SkyePooley/ENEL599-Final-Project/Images/20231011_123835.jpg

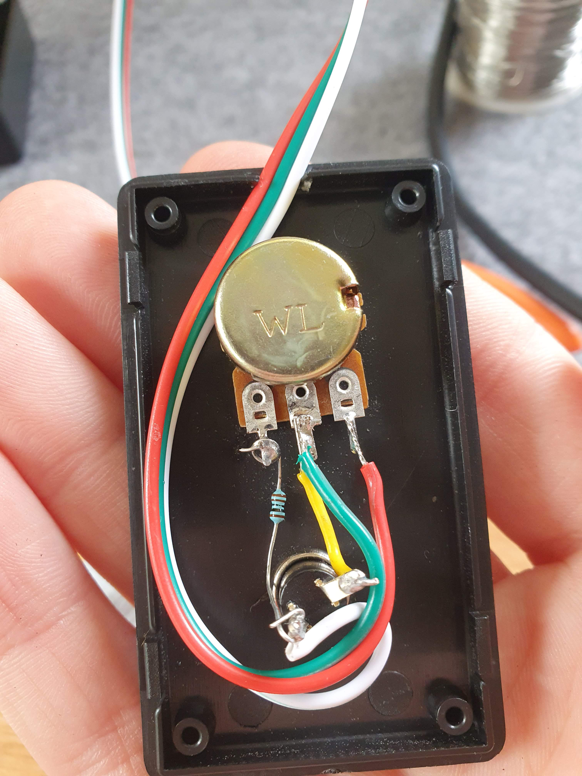
Images/20231011_123835.jpg
