SkyePooley/ENEL599-Final-Project/Images/20231019_002048.jpg

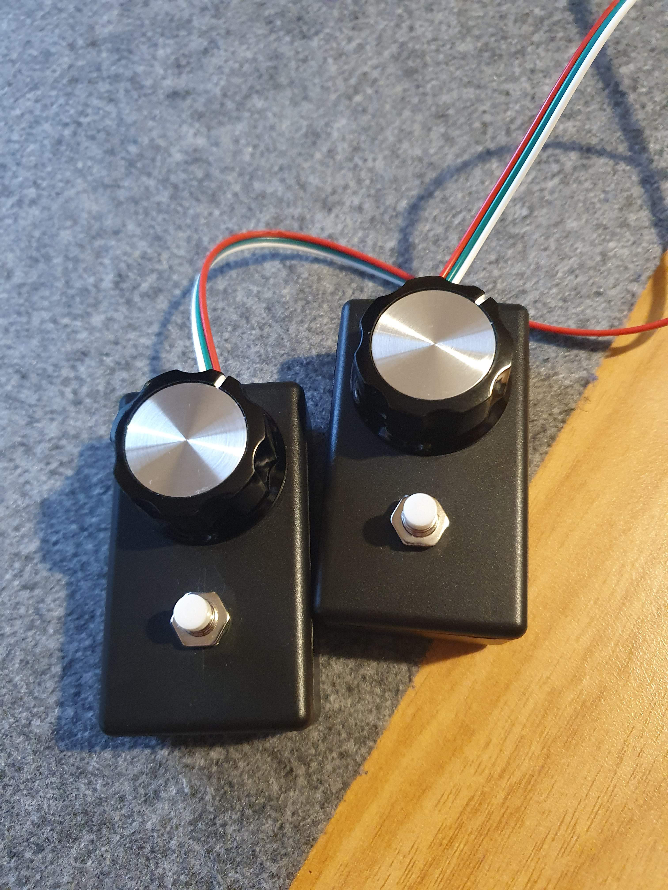
Images/20231019_002048.jpg
