SkyePooley/ENEL599-Final-Project/Images/20231019_221137.jpg

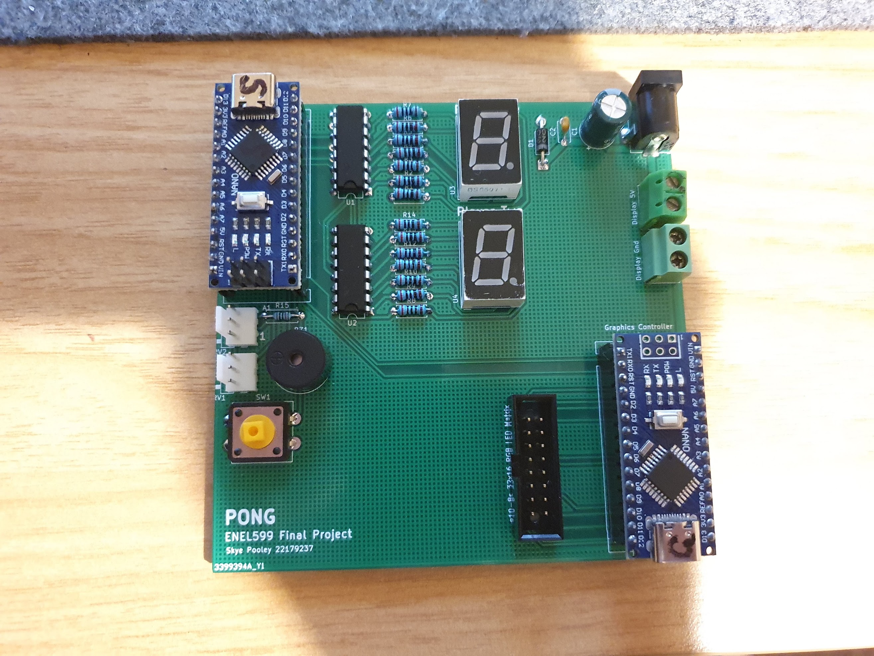
Images/20231019_221137.jpg
