SkyePooley/ENEL599-Final-Project/Final Project KiCAD designs/Final Project KiCAD designs.kicad_sch

## KiCad design Final Project KiCAD designs/Final Project KiCAD designs.kicad_sch (2023-10-18, an earlier design)

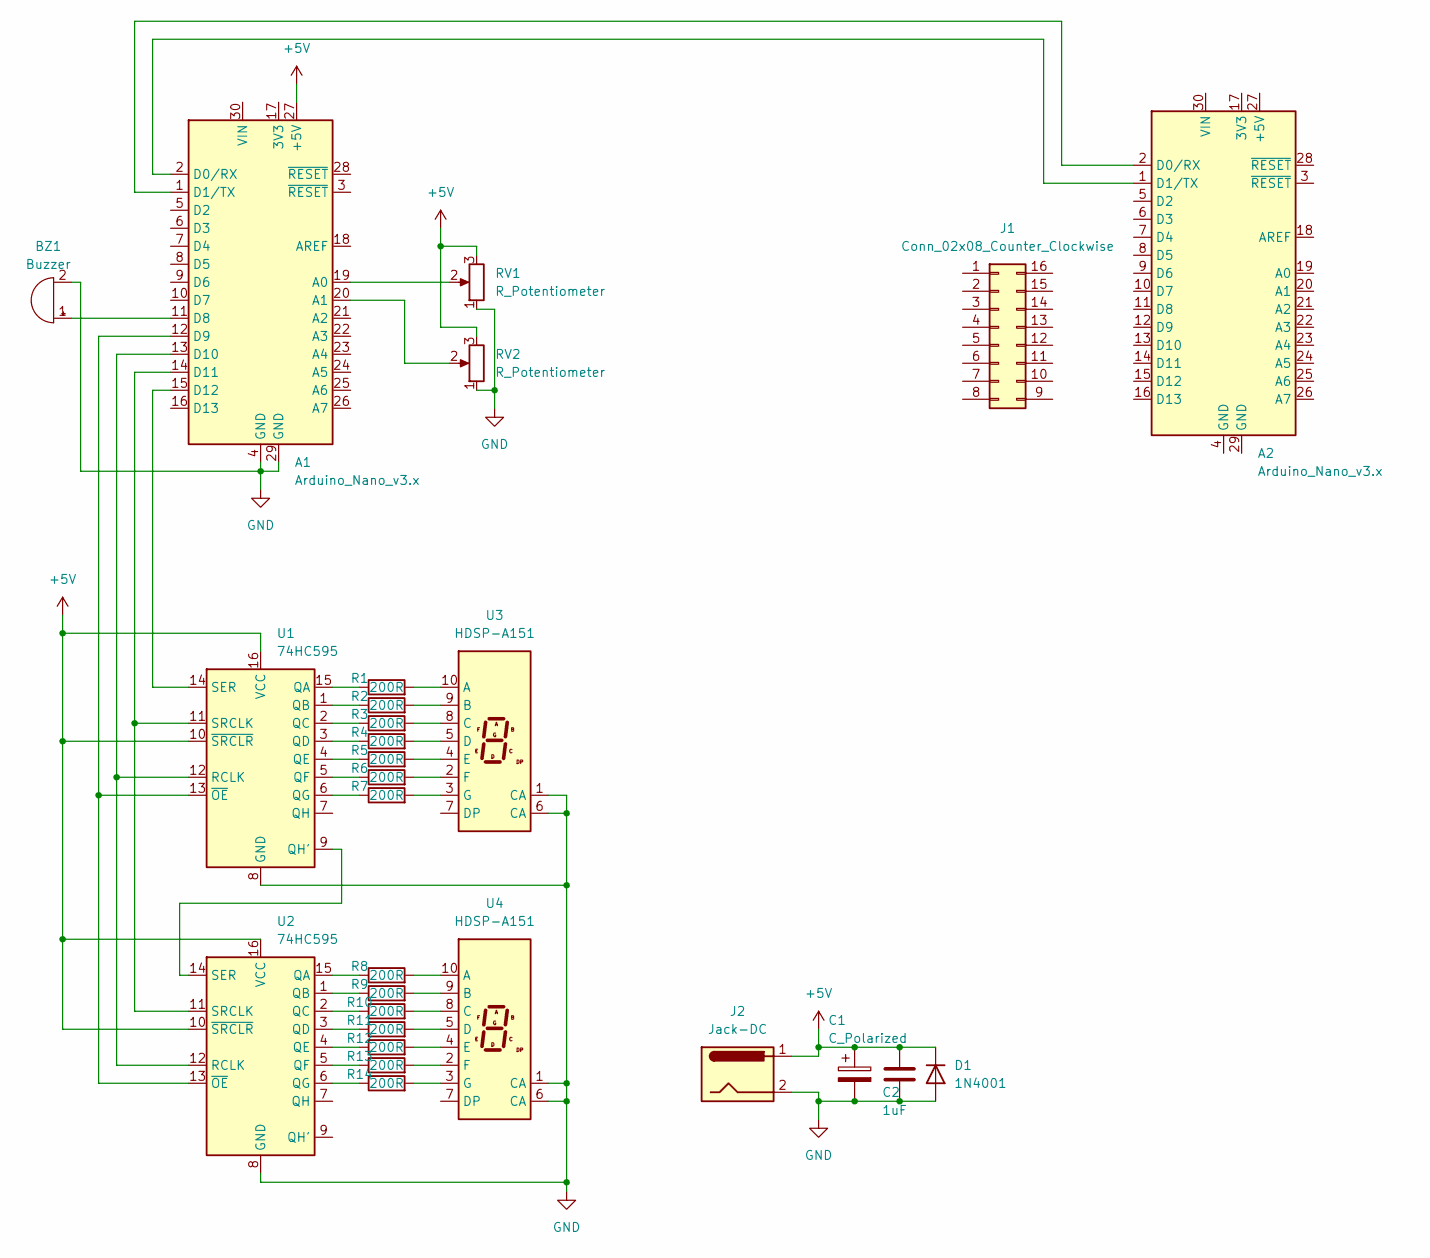
[picture p16: schematic Final Project KiCAD designs.kicad_sch]

Parts:
A1, A2: Arduino_Nano_v3.x; Arduino_Nano
BZ1: Buzzer
C1: C_Polarized
C2: 1uF
D1: 1N4001; D_DO-41_SOD81_P10.16mm_Horizontal
J1: Conn_02x08_Counter_Clockwise
J2: Jack-DC
R1, R2, R3, R4, R5, R6, R7, R8, R9, R10, R11, R12, R13, R14: 200R
RV1, RV2: R_Potentiometer
U1, U2: 74HC595
U3, U4: HDSP-A151

Connections:
+5V: A1.27 (+5V), C1.1, C2.1, D1.1 (K), J2.1, RV1.3, RV2.3, U1.10 (~SRCLR), U1.16 (VCC), U2.10 (~SRCLR), U2.16 (VCC)
GND: A1.4 (GND), A1.29 (GND), BZ1.2 (+), C1.2, C2.2, D1.2 (A), J2.2, RV1.1, RV2.1, U1.8 (GND), U2.8 (GND), U3.1 (CA), U3.6 (CA), U4.1 (CA), U4.6 (CA)
unnamed: A1.1 (D1/TX), A2.2 (D0/RX)
unnamed: A1.2 (D0/RX), A2.1 (D1/TX)
unnamed: A1.11 (D8), BZ1.1 (-)
unnamed: A1.12 (D9), U1.13 (~OE), U2.13 (~OE)
unnamed: A1.13 (D10), U1.12 (RCLK), U2.12 (RCLK)
unnamed: A1.14 (D11), U1.11 (SRCLK), U2.11 (SRCLK)
unnamed: A1.15 (D12), U1.14 (SER)
unnamed: A1.19 (A0), RV1.2
unnamed: A1.20 (A1), RV2.2
unnamed: R1.1, U1.15 (QA)
unnamed: R1.2, U3.10 (A)
unnamed: R2.1, U1.1 (QB)
unnamed: R2.2, U3.9 (B)
unnamed: R3.1, U1.2 (QC)
unnamed: R3.2, U3.8 (C)
unnamed: R4.1, U1.3 (QD)
unnamed: R4.2, U3.5 (D)
unnamed: R5.1, U1.4 (QE)
unnamed: R5.2, U3.4 (E)
unnamed: R6.1, U1.5 (QF)
unnamed: R6.2, U3.2 (F)
unnamed: R7.1, U1.6 (QG)
unnamed: R7.2, U3.3 (G)
unnamed: R8.1, U2.15 (QA)
unnamed: R8.2, U4.10 (A)
unnamed: R9.1, U2.1 (QB)
unnamed: R9.2, U4.9 (B)
unnamed: R10.1, U2.2 (QC)
unnamed: R10.2, U4.8 (C)
unnamed: R11.1, U2.3 (QD)
unnamed: R11.2, U4.5 (D)
unnamed: R12.1, U2.4 (QE)
unnamed: R12.2, U4.4 (E)
unnamed: R13.1, U2.5 (QF)
unnamed: R13.2, U4.2 (F)
unnamed: R14.1, U2.6 (QG)
unnamed: R14.2, U4.3 (G)
unnamed: U1.9 (QH'), U2.14 (SER)
