SkyePooley/ENEL599-Final-Project/paddledraw/paddledraw_copy_20231004115806.ino

#include <RGBmatrixPanel.h>

#define CLK  8   // USE THIS ON ARDUINO UNO, ADAFRUIT METRO M0, etc.
#define OE   9
#define LAT 10
#define A   A0
#define B   A2
#define C   A1
#define POT A4

static int targetRefreshRate = 10;
static int frameTime = 1000 / targetRefreshRate;
static int paddleDimensions[2] = {1,4}; // x,y

RGBmatrixPanel matrix(A, B, C, CLK, LAT, OE, false);

// Timers
unsigned long lastDrawnTime = millis();
unsigned long timeStamp = millis();

int paddlePosition = 0;
float ballPosition[2] = {0, 0}; // 0-31, 0-15
int ballDirection = 135; // Ball travel direction in degrees, 0 is straight up.

void drawFrame(int paddleAPos){
    matrix.fillScreen(matrix.Color333(0, 0, 0));
    matrix.fillRect(0, paddleAPos, paddleDimensions[0], paddleDimensions[1], matrix.Color333(7, 0, 0));
}

// void updateBall(float ballPos[], ballDirection) {

// }

void setup() {
  pinMode(OE, OUTPUT);
  pinMode(LAT, OUTPUT);
  pinMode(A, OUTPUT);
  pinMode(B, OUTPUT);
  pinMode(C, OUTPUT);
  pinMode(CLK, OUTPUT);

  matrix.begin();
  matrix.fillScreen(matrix.Color333(0, 0, 0));
  pinMode(POT, INPUT);
}

void loop() {
    if (millis() - timeStamp > 200) {
        paddlePosition ++;
        if (paddlePosition > 15)
            paddlePosition = 0;
        timeStamp = millis();
    }

    // Refresh the frame on time.
    if (millis() - lastDrawnTime > frameTime) {
        drawFrame(paddlePosition);
    }
    
  
}
